deltaphi/c6021light/c6021light/doc/images/c6021light_with_PSU.jpg

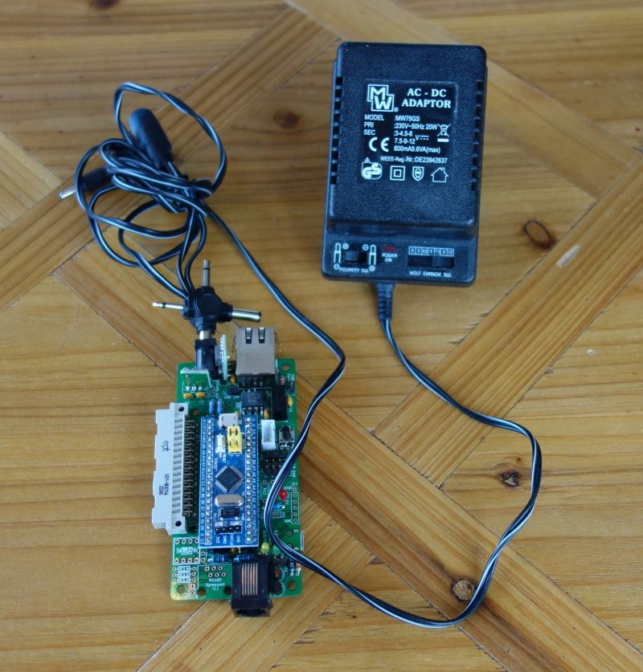
c6021light/doc/images/c6021light_with_PSU.jpg
