deltaphi/c6021light/c6021light/doc/images/Keyboard6040.jpg

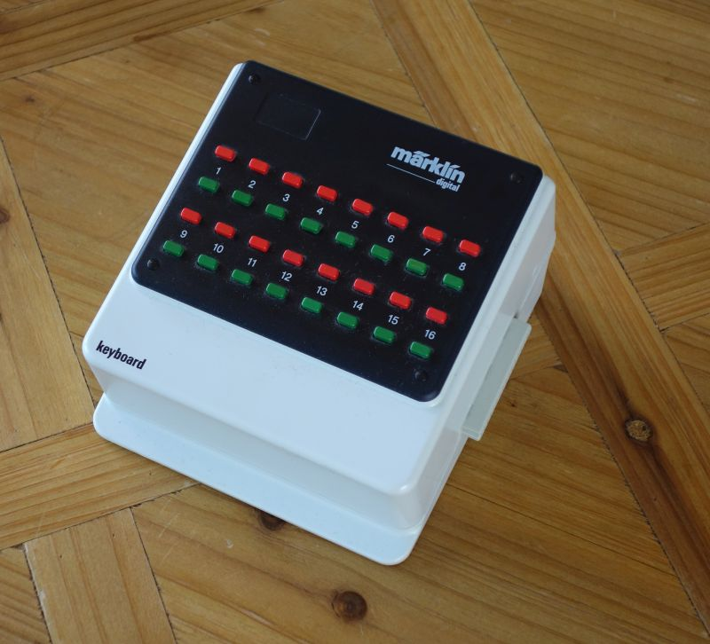
c6021light/doc/images/Keyboard6040.jpg
