deltaphi/c6021light/c6021light/doc/images/ms2_gleisbox_srseii.jpg

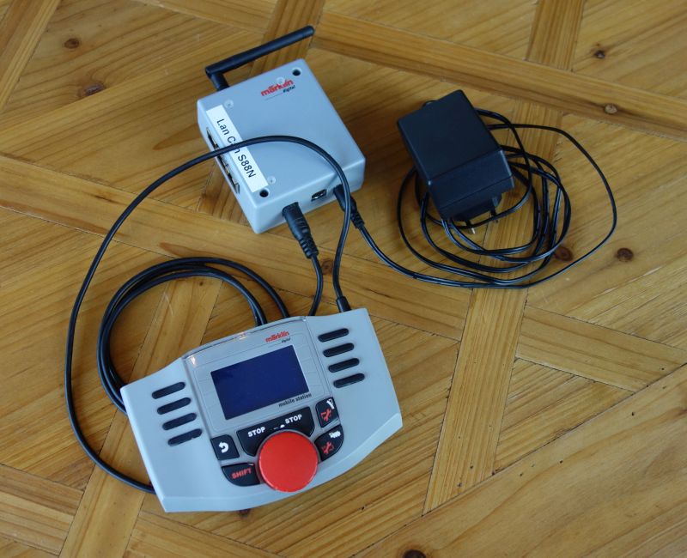
c6021light/doc/images/ms2_gleisbox_srseii.jpg
