deltaphi/c6021light/c6021light/doc/images/ms2_loco_go.jpg

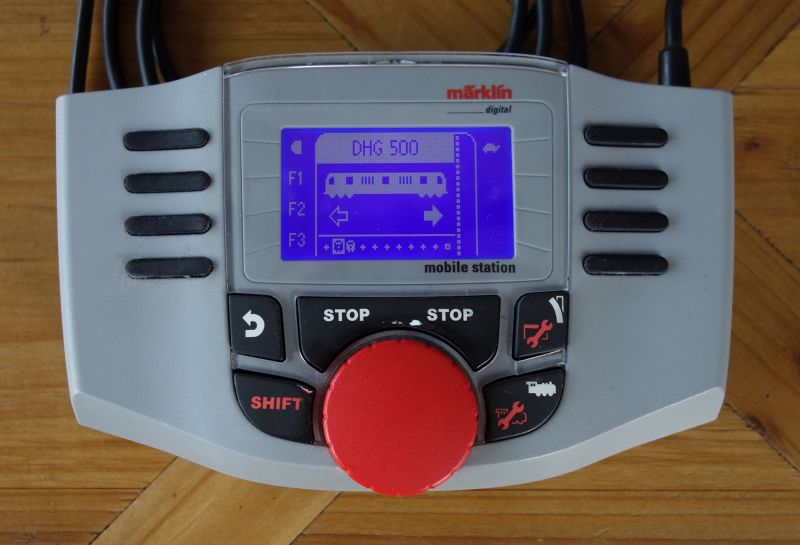
c6021light/doc/images/ms2_loco_go.jpg
