deltaphi/c6021light/c6021light/doc/images/ms2_loco_stop.jpg

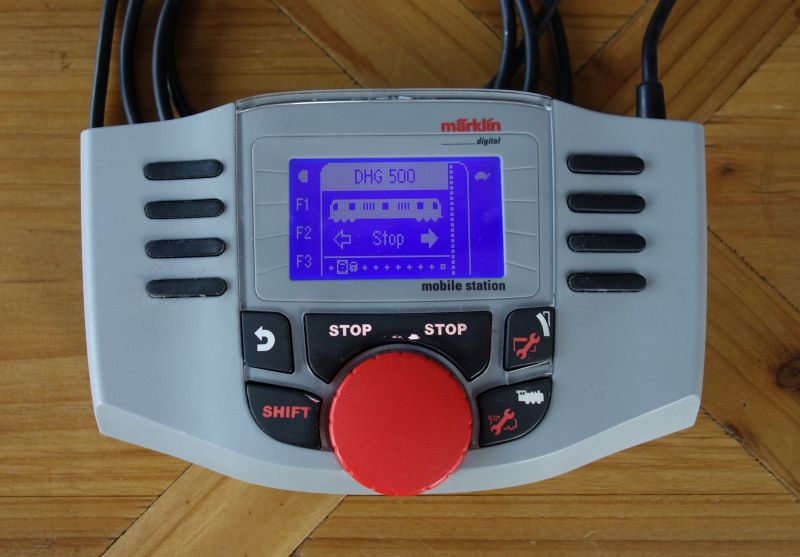
c6021light/doc/images/ms2_loco_stop.jpg
