deltaphi/c6021light/c6021light/doc/images/ms2_turnout_go.jpg

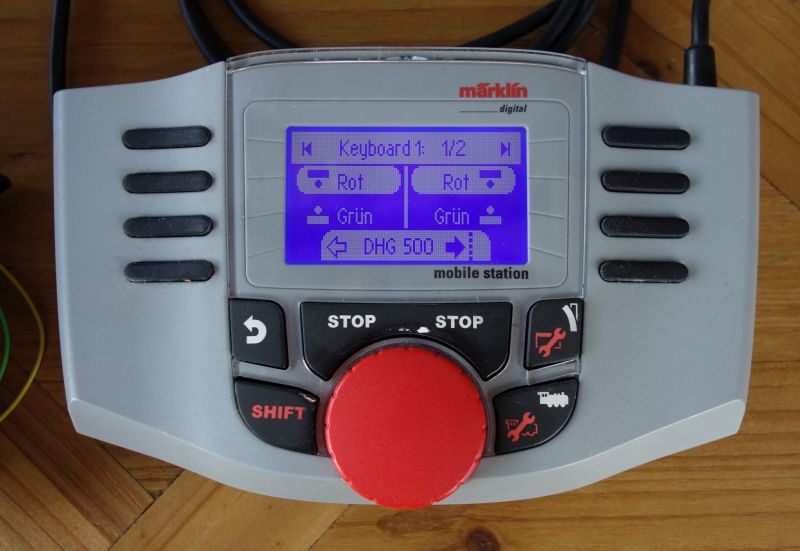
c6021light/doc/images/ms2_turnout_go.jpg
