deltaphi/c6021light/pictures/board_01.jpg

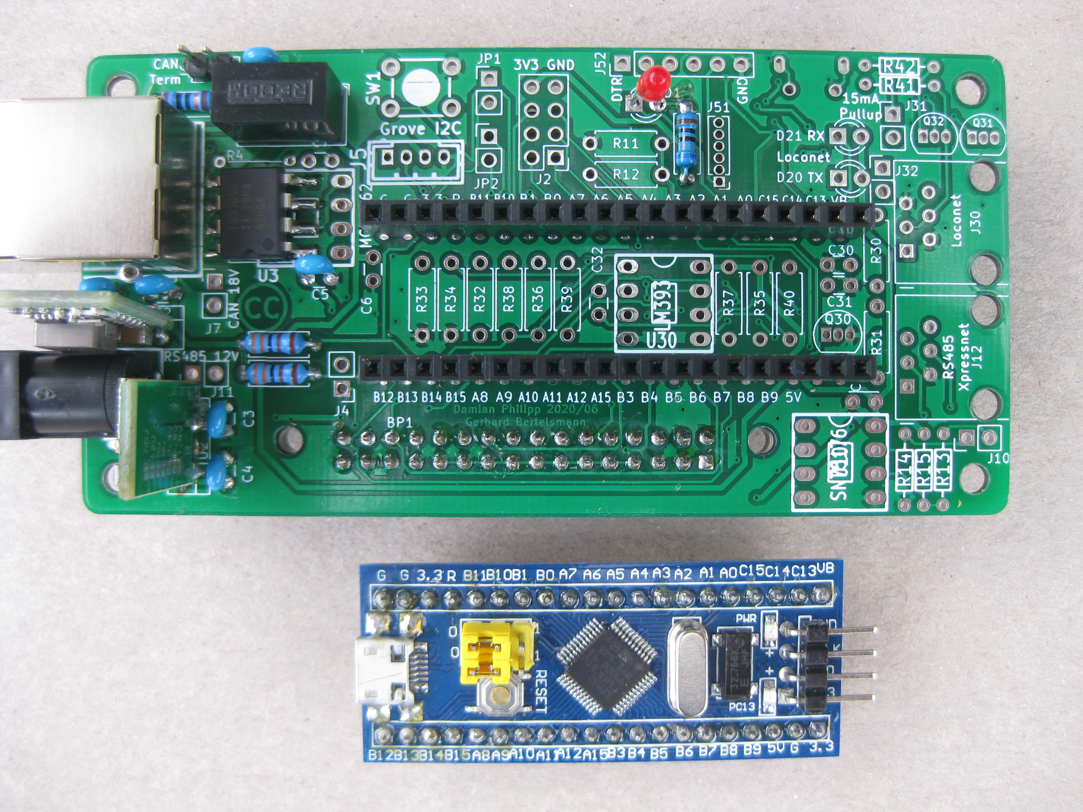
pictures/board_01.jpg
