deltaphi/c6021light/c6021light/src/tasks/RoutingTask/CanEngineDBStateMachine.h

#ifndef __TASKS__ROUTINGTASK__CANENGINEDBSTATEMACHINE_H__
#define __TASKS__ROUTINGTASK__CANENGINEDBSTATEMACHINE_H__

#include "tasks/RoutingTask/CanEngineDB.h"
#include "tasks/RoutingTask/StateMachineBase.h"

#include "IStatusIndicator.h"

namespace tasks {
namespace RoutingTask {

/*
 * \brief Class CanEngineDBStateMachine
 */
class CanEngineDBStateMachine : public StateMachineBase {
 public:
  constexpr static const uint8_t kMaxDownloadTries = 10;

  enum class RequestState { IDLE, REQUESTING, DOWNLOADING };

  CanEngineDBStateMachine(CanEngineDB& engineDb, freertossupport::OsTask& parentTask)
      : StateMachineBase(parentTask), engineDb_(engineDb) {}

  void startRequesting() {
    requestState_ = RequestState::REQUESTING;
    if (statusIndicator != nullptr) {
      statusIndicator->setCanDbDownload();
    }
    tries = 0;
    startTimerImmediate();
  }

  void loop() {
    if (timerExpired_) {
      if (requestState_ == RequestState::REQUESTING) {
        if (tries < kMaxDownloadTries) {
          RR32Can::RR32Can.AbortCurrentConfigRequest();
          engineDb_.fetchEngineDB();
          ++tries;
        } else {
          stopRequesting();
        }
      }
      timerExpired_ = false;
    }
  }

  bool isIdle() { return requestState_ == RequestState::IDLE; }

  RequestState GetState() const { return requestState_; }

  void handlePacket(RR32Can::CanFrame& frame) {
    if (!isIdle() && isFirstPacketInConfigDataStream(frame)) {
      requestState_ = RequestState::DOWNLOADING;
    }
  }

  void notifyEngineDBComplete() {
    if (!isIdle()) {
      stopRequesting();
    }
  }

  void setStatusIndicator(IStatusIndicator& si) { this->statusIndicator = &si; }

 private:
  RequestState requestState_{RequestState::IDLE};
  uint8_t tries = 0;
  CanEngineDB& engineDb_;
  IStatusIndicator* statusIndicator{nullptr};

  void stopRequesting() {
    requestState_ = RequestState::IDLE;
    stopTimer();
    if (statusIndicator != nullptr) {
      statusIndicator->clearCanDbDownload();
    }
  }

  bool isFirstPacketInConfigDataStream(RR32Can::CanFrame& frame) {
    return (frame.id.getCommand() == RR32Can::Command::CONFIG_DATA_STREAM) &&
           (frame.data.dlc == 6 || frame.data.dlc == 7);
  }
};

}  // namespace RoutingTask
}  // namespace tasks

#endif  // __TASKS__ROUTINGTASK__CANENGINEDBSTATEMACHINE_H__
