deltaphi/c6021light/c6021light/src/tasks/RoutingTask/RoutingTask.cpp

#include "tasks/RoutingTask/RoutingTask.h"

#include <cstdio>

#include <LocoNet.h>
#include "RR32Can/RR32Can.h"
#include "hal/stm32I2C.h"
#include "hal/stm32can.h"
#include "tasks/RoutingTask/LocoNetPrinter.h"

#include "DataModel.h"

namespace tasks {
namespace RoutingTask {

void RoutingTask::processCAN() {
  for (auto framePtr = hal::getCanMessage(); framePtr != nullptr; framePtr = hal::getCanMessage()) {
    i2cForwarder_.forward(*framePtr);
    lnForwarder_.forward(*framePtr);
    // Forward to self
    RR32Can::RR32Can.HandlePacket(*framePtr);
    stopGoStateM_.handlePacket(*framePtr);
    canEngineDBStateM_.handlePacket(*framePtr);
    // Explicitly reset framePtr so that getCanMessage can produce a new message
    framePtr.reset();
  }

  // Attempt to forward all updates in the CAN DB
  if (!slotServer_.isDisabled()) {
    for (auto& locoEntry : engineDb_) {
      if (locoEntry.hasUpdate()) {
        lnForwarder_.forwardLocoChange(locoEntry.loco, locoEntry.diff);
      }
    }
  }
}

void RoutingTask::processI2CMessages() {
  for (auto messagePtr = hal::getI2CMessage(); messagePtr != nullptr;
       messagePtr = hal::getI2CMessage()) {
    printf("I2C RX: ");
    messagePtr->print(true);

    RR32Can::CanFrame frame;

    // Convert to generic CAN representation
    if (i2cForwarder_.MakeRR32CanMsg(*messagePtr, frame)) {
      RR32Can::RR32Can.SendPacket(frame);
      lnForwarder_.forward(frame);
      // Forward to self
      RR32Can::RR32Can.HandlePacket(frame);
    }

    i2cForwarder_.sendI2CResponseIfEnabled(*messagePtr);

    // Explicitly reset messagePtr so that getI2CMessage can produce a new message
    messagePtr.reset();
  }
}

void RoutingTask::processI2CStopGo() {
  RR32Can::CanFrame frame;
  if (i2cForwarder_.MakeRR32CanPowerMsg(hal::getStopGoRequest(), frame)) {
    RR32Can::RR32Can.SendPacket(frame);
    lnForwarder_.forward(frame);
    // Forward to self
    RR32Can::RR32Can.HandlePacket(frame);
  }
}

void RoutingTask::processLocoNet() {
  for (lnMsg* LnPacket = LocoNet.receive(); LnPacket; LnPacket = LocoNet.receive()) {
    printLnPacket(*LnPacket, RxTxDirection::RX);

    RR32Can::CanFrame frame;

    // Convert to generic CAN representation
    if (lnForwarder_.MakeRR32CanMsg(*LnPacket, frame)) {
      i2cForwarder_.forward(frame);
      // Forward to CAN
      RR32Can::RR32Can.SendPacket(frame);

      // Forward to self
      RR32Can::RR32Can.HandlePacket(frame);
    }
    lnForwarder_.HandleDummyMessages(*LnPacket);
    slotServer_.process(*LnPacket);
  }
}

void RoutingTask::processStateMachines() {
  stopGoStateM_.loop();

  if (engineDb_.isComplete()) {
    canEngineDBStateM_.notifyEngineDBComplete();
  }
  canEngineDBStateM_.loop();
}

void RoutingTask::matchEnginesFromLocoNetAndCan() {
  if (!slotServer_.isDisabled()) {
    for (auto& locoEntry : slotServer_) {
      // See if the engine needs a match to CAN
      if (locoEntry.needsMatchToCAN) {
        const auto enginePtr = engineDb_.findEngine(locoEntry.loco.getAddress());
        if (enginePtr != nullptr) {
          locoEntry.loco.setUid(enginePtr->getUid());
        }
      }

      // Attempt to forward all updates in the Slot server
      if (locoEntry.hasUpdate()) {
        canForwarder_.forwardLocoChange(locoEntry.loco, locoEntry.diff);
      }
    }
  }
}

void RoutingTask::loop() {
  processI2CStopGo();
  processCAN();
  processI2CMessages();
  processLocoNet();
  processStateMachines();
  matchEnginesFromLocoNetAndCan();
}

/**
 * \brief When a message was received, create and send a response message.
 */
void RoutingTask::TaskMain() {
  while (1) {
    waitForNotify();
    loop();
  }
}

}  // namespace RoutingTask
}  // namespace tasks
