deltaphi/c6021light/c6021light/src/tasks/RoutingTask/RoutingTask.h

#ifndef __TASKS__ROUTINGTASK__ROUTINGTASK_H__
#define __TASKS__ROUTINGTASK__ROUTINGTASK_H__

#include "MarklinI2C/Messages/AccessoryMsg.h"

#include "DataModel.h"

#include "OsTask.h"

#include "CANForwarder.h"
#include "I2CForwarder.h"
#include "LocoNetForwarder.h"

#include "CanEngineDB.h"
#include "CanEngineDBStateMachine.h"
#include "LocoNetSlotServer.h"
#include "StopGoStateMachine.h"

namespace tasks {
namespace RoutingTask {

class RoutingTask : public freertossupport::OsTask {
 public:
  static constexpr const uint32_t kStackSize = 256;

  void begin(DataModel& dataModel, LocoNetTx& lnTx, freertossupport::OsTimer& stopGoTimer,
             freertossupport::OsTimer& canEngineDBTimer, IStatusIndicator& statusIndicator) {
    lnForwarder_.init(dataModel, slotServer_, lnTx);
    i2cForwarder_.init(dataModel);
    slotServer_.init(dataModel, lnTx);
    engineDb_.init(statusIndicator);
    stopGoStateM_.setTimer(stopGoTimer);
    canEngineDBStateM_.setTimer(canEngineDBTimer);
    canEngineDBStateM_.setStatusIndicator(statusIndicator);
  };

  void TaskMain();
  void loop();

  const LocoNetSlotServer& getLnSlotServer() const { return slotServer_; }
  LocoNetSlotServer& getLnSlotServer() { return slotServer_; }

  CanEngineDB& getCANEngineDB() { return engineDb_; }

 private:
  LocoNetSlotServer slotServer_;
  CanEngineDB engineDb_;

  CANForwarder canForwarder_;
  I2CForwarder i2cForwarder_;
  LocoNetForwarder lnForwarder_;

  void processCAN();
  void processI2CMessages();
  void processI2CStopGo();
  void processLocoNet();
  void matchEnginesFromLocoNetAndCan();

  void processStateMachines();

 public:
  StopGoStateMachine stopGoStateM_{canForwarder_, *this};
  CanEngineDBStateMachine canEngineDBStateM_{engineDb_, *this};
};

}  // namespace RoutingTask
}  // namespace tasks

#endif  // __TASKS__ROUTINGTASK__ROUTINGTASK_H__
