deltaphi/c6021light/c6021light/src/tasks/RoutingTask/CanEngineDB.h

#ifndef __TASKS__ROUTINGTASK__CANENGINEDB_H__
#define __TASKS__ROUTINGTASK__CANENGINEDB_H__

#include <array>
#include "RR32Can/Locomotive.h"
#include "RR32Can/callback/EngineCbk.h"
#include "RR32CanEngineDb/LocoConsumer.h"
#include "RR32CanEngineDb/LocoListConsumer.h"
#include "RR32CanEngineDb/util/ConfigDataConsumer.h"
#include "RR32CanEngineDb/util/ConfigDataEndStreamCallback.h"
#include "RR32CanEngineDb/util/ConfigDataStreamParser.h"

#include "IStatusIndicator.h"
#include "RoutingForwarder.h"

namespace tasks {
namespace RoutingTask {

/*
 * \brief Class CanEngineDB
 */
class CanEngineDB : public RR32Can::ConfigDataEndStreamCallback,
                    public RR32Can::callback::EngineCbk {
 public:
  constexpr static const uint8_t kMaxNumDbEntries = 40;

  struct DbEntry_t {
    RR32Can::Locomotive loco;
    LocoDiff_t diff;

    void reset() {
      loco.reset();
      diff = LocoDiff_t();
    }

    bool hasUpdate() const { return diff.hasDiff(); }
  };

  void init(IStatusIndicator& si) { this->statusIndicator = &si; }

  using DB_t = std::array<DbEntry_t, kMaxNumDbEntries>;

  enum class DBState { EMPTY, DOWNLOADING, COMPLETE };

  void fetchEngineDB();

  void streamComplete(RR32Can::ConfigDataConsumer*) override;
  void streamAborted(RR32Can::ConfigDataConsumer*) override {}

  void dump() const;

  // Overrides for EngineCbk
  void setLocoVelocity(RR32Can::Locomotive::Uid_t engineUid, RR32Can::Velocity_t velocity) override;
  void setLocoVelocity(RR32Can::Velocity_t velocity) override;
  void setLocoFunction(const RR32Can::Uid_t engineUid, uint8_t functionIdx,
                       bool functionOn) override;
  void setLocoDirection(const RR32Can::Uid_t engineUid,
                        const RR32Can::EngineDirection direction) override;
  void changeLocoDirection(const RR32Can::Uid_t engineUid) override;

  auto begin() { return db_.begin(); }
  auto end() { return db_.end(); }

  const RR32Can::Locomotive* findEngine(const RR32Can::Locomotive::Address_t address) const {
    for (auto& entry : db_) {
      if (entry.loco.isFullDetailsKnown() && (address == entry.loco.getAddress())) {
        return &entry.loco;
      }
    }
    return nullptr;
  }

  bool isEmpty() const { return dbState_ == DBState::EMPTY; }
  bool isDownloading() const { return dbState_ == DBState::DOWNLOADING; }
  bool isComplete() const { return dbState_ == DBState::COMPLETE; }

 private:
  RR32Can::ConfigDataStreamParser streamParser_;
  RR32Can::LocoListConsumer listConsumer_;
  RR32Can::LocoConsumer locoConsumer_;
  DB_t db_;
  DBState dbState_{DBState::EMPTY};
  IStatusIndicator* statusIndicator{nullptr};

  DB_t::iterator getEntry(const RR32Can::Locomotive::Uid_t uid);
  RR32Can::Locomotive* findFirstIncompleteEngine();

  void fetchEnginesFromOffset(uint8_t offset);

  void fetchEngine(RR32Can::Locomotive& loco);
  void fetchNextEngine();

  bool hasEngine(const char* const engineName) const;
};

}  // namespace RoutingTask
}  // namespace tasks

#endif  // __TASKS__ROUTINGTASK__CANENGINEDB_H__
