deltaphi/c6021light/c6021light/src/tasks/RoutingTask/LocoNetPrinter.h

#ifndef __TASKS__ROUTINGTASK__LOCONETPRINTER_H__
#define __TASKS__ROUTINGTASK__LOCONETPRINTER_H__

#include <LocoNet.h>

namespace tasks {
namespace RoutingTask {

enum class RxTxDirection { RX, TX };

void printLnPacket(const lnMsg& LnPacket, RxTxDirection rxTx);

}  // namespace RoutingTask
}  // namespace tasks

#endif  // __TASKS__ROUTINGTASK__LOCONETPRINTER_H__
