deltaphi/c6021light/c6021light/src/LocoNetTx.h

#ifndef __LOCONETTX_H__
#define __LOCONETTX_H__

#include <ln_opc.h>

#include <AtomicRingBuffer/ObjectRingBuffer.h>

/*
 * \brief Class LocoNetTx
 */
class LocoNetTx {
 public:
  constexpr static const uint8_t QueueDepth = 8;

  /**
   * \brief Queue a message for asynchronous transmission.
   *
   * Message may be dropped if the buffer is full.
   *
   * \return true if the message was enqueued, false otherwise.
   */
  bool AsyncSend(const lnMsg& msg);

  /**
   * \brief Perform the acutal blocking send operation for a queued message.
   */
  void DoBlockingSend();

 private:
  AtomicRingBuffer::ObjectRingBuffer<lnMsg, QueueDepth> msgBuffer_;
};

#endif  // __LOCONETTX_H__
