deltaphi/c6021light/c6021light/test/integration/EngineRouting.cpp

#include "gmock/gmock.h"
#include "gtest/gtest.h"

#include "tasks/RoutingTask/LocoNetSlotServer.h"

#include "mocks/RoutingTaskFixture.h"

#include "mocks/SequenceMaker.h"

class EngineRoutingFixture : public mocks::RoutingTaskFixture {
 public:
  void SetUp() {
    mocks::RoutingTaskFixture::SetUp();

    exampleLoco_.setUid(0x101010);
    exampleLoco_.setAddress(RR32Can::util::MM2_Loco(42U));
    exampleLoco_.setName("BR 42");
    exampleLoco_.setAvailability(RR32Can::LocomotiveShortInfo::AvailabilityStatus::FULL_DETAILS);

    dataModel.lnSlotServerState = tasks::RoutingTask::LocoNetSlotServer::SlotServerState::PASSIVE;

    {
      auto slotIt =
          routingTask.getLnSlotServer().findOrAllocateSlotForAddress(exampleLoco_.getAddress());
      ASSERT_NE(slotIt, routingTask.getLnSlotServer().end());
      slotIt->loco = exampleLoco_;
      slotIt->inUse = true;
      slotIt->needsMatchToCAN = true;
    }

    {
      auto engineIt = routingTask.getCANEngineDB().begin();
      engineIt->loco = exampleLoco_;
    }
  }

  RR32Can::Locomotive exampleLoco_;
  const uint8_t kLocoSlotIdx = 1;
};

namespace tasks {
namespace RoutingTask {

TEST_F(EngineRoutingFixture, SpeedChangeCanToLn) {
  RR32Can::CanFrame injectedMessage = RR32Can::util::LocoSpeed(false, exampleLoco_.getUid(), 500);
  lnMsg expectedMessage = Ln_LocoSpeed(kLocoSlotIdx, 500);

  mocks::makeSequence(i2cHal);
  EXPECT_CALL(i2cHal, getStopGoRequest()).WillOnce(Return(hal::StopGoRequest{}));
  mocks::makeSequence(lnHal);
  mocks::makeSequence(canHal, injectedMessage);

  EXPECT_CALL(lnTx, DoAsyncSend(expectedMessage));

  routingTask.loop();
}

TEST_F(EngineRoutingFixture, SpeedChangeLnToCan) {
  RR32Can::CanFrame expectedMessage = RR32Can::util::LocoSpeed(false, exampleLoco_.getUid(), 496);
  lnMsg injetedMessage = Ln_LocoSpeed(kLocoSlotIdx, 496);

  mocks::makeSequence(i2cHal);
  EXPECT_CALL(i2cHal, getStopGoRequest()).WillOnce(Return(hal::StopGoRequest{}));
  mocks::makeSequence(lnHal, injetedMessage);
  mocks::makeSequence(canHal);

  EXPECT_CALL(canTx, SendPacket(expectedMessage));

  routingTask.loop();
}

TEST_F(EngineRoutingFixture, DirectionChangeCanToLn) {
  RR32Can::CanFrame injectedMessage =
      RR32Can::util::LocoDirection(false, exampleLoco_.getUid(), RR32Can::EngineDirection::REVERSE);
  RR32Can::Locomotive updatedLoco = exampleLoco_;
  updatedLoco.setDirection(RR32Can::EngineDirection::REVERSE);
  ASSERT_NE(updatedLoco.getDirection(), exampleLoco_.getDirection());
  lnMsg expectedMessage = Ln_LocoDirf(kLocoSlotIdx, updatedLoco);

  mocks::makeSequence(i2cHal);
  EXPECT_CALL(i2cHal, getStopGoRequest()).WillOnce(Return(hal::StopGoRequest{}));
  mocks::makeSequence(lnHal);
  mocks::makeSequence(canHal, injectedMessage);

  EXPECT_CALL(lnTx, DoAsyncSend(expectedMessage));

  routingTask.loop();
}

TEST_F(EngineRoutingFixture, DirectionChangeLnToCan) {
  RR32Can::CanFrame expectedMessage =
      RR32Can::util::LocoDirection(false, exampleLoco_.getUid(), RR32Can::EngineDirection::REVERSE);
  RR32Can::Locomotive updatedLoco = exampleLoco_;
  updatedLoco.setDirection(RR32Can::EngineDirection::REVERSE);
  ASSERT_NE(updatedLoco.getDirection(), exampleLoco_.getDirection());
  lnMsg injetedMessage = Ln_LocoDirf(kLocoSlotIdx, updatedLoco);

  mocks::makeSequence(i2cHal);
  EXPECT_CALL(i2cHal, getStopGoRequest()).WillOnce(Return(hal::StopGoRequest{}));
  mocks::makeSequence(lnHal, injetedMessage);
  mocks::makeSequence(canHal);

  EXPECT_CALL(canTx, SendPacket(expectedMessage));

  routingTask.loop();
}

using FunctionFixtureParam_t = uint8_t;

class EngineRoutingFunctionFixture : public EngineRoutingFixture,
                                     public WithParamInterface<FunctionFixtureParam_t> {
 public:
  void SetUp() {
    EngineRoutingFixture::SetUp();

    const auto functionIdx = GetParam();

    canFrame = RR32Can::util::LocoFunction(false, exampleLoco_.getUid(), functionIdx, true);

    RR32Can::Locomotive updatedLoco = exampleLoco_;
    updatedLoco.setFunction(functionIdx, true);
    ASSERT_NE(updatedLoco.getFunction(functionIdx), exampleLoco_.getFunction(functionIdx));

    if (functionIdx < 5) {
      locoNetMessage = Ln_LocoDirf(kLocoSlotIdx, updatedLoco);
    } else if (functionIdx < 9) {
      locoNetMessage = Ln_LocoSnd(kLocoSlotIdx, updatedLoco);
    } else if (functionIdx < 13) {
      locoNetMessage = Ln_LocoSnd2(kLocoSlotIdx, updatedLoco);
    } else if (functionIdx < 20) {
      locoNetMessage = Ln_LocoFunExt(kLocoSlotIdx, LocoFunExtBlockId::FIRST, updatedLoco);
    } else if (functionIdx == 20 || functionIdx == 28) {
      locoNetMessage = Ln_LocoFunExt(kLocoSlotIdx, LocoFunExtBlockId::THIRD, updatedLoco);
    } else if (functionIdx < 28) {
      locoNetMessage = Ln_LocoFunExt(kLocoSlotIdx, LocoFunExtBlockId::SECOND, updatedLoco);
    } else {
      FAIL() << "Parameter '" << functionIdx << "' not implemented.";
    }
  }

  RR32Can::CanFrame canFrame;
  lnMsg locoNetMessage;
};

TEST_P(EngineRoutingFunctionFixture, FunctionChangeCanToLn) {
  mocks::makeSequence(i2cHal);
  EXPECT_CALL(i2cHal, getStopGoRequest()).WillOnce(Return(hal::StopGoRequest{}));
  mocks::makeSequence(lnHal);
  mocks::makeSequence(canHal, canFrame);

  EXPECT_CALL(lnTx, DoAsyncSend(locoNetMessage));

  routingTask.loop();
}

TEST_P(EngineRoutingFunctionFixture, FunctionChangeLnToCan) {
  mocks::makeSequence(i2cHal);
  EXPECT_CALL(i2cHal, getStopGoRequest()).WillOnce(Return(hal::StopGoRequest{}));
  mocks::makeSequence(lnHal, locoNetMessage);
  mocks::makeSequence(canHal);

  EXPECT_CALL(canTx, SendPacket(canFrame));

  routingTask.loop();
}

INSTANTIATE_TEST_SUITE_P(EngineRoutingFunctions, EngineRoutingFunctionFixture,
                         Range(static_cast<FunctionFixtureParam_t>(0U),
                               static_cast<FunctionFixtureParam_t>(29U)));

}  // namespace RoutingTask
}  // namespace tasks
